waveform80/blinkenxmas/blinkenxmas/no-preview.png

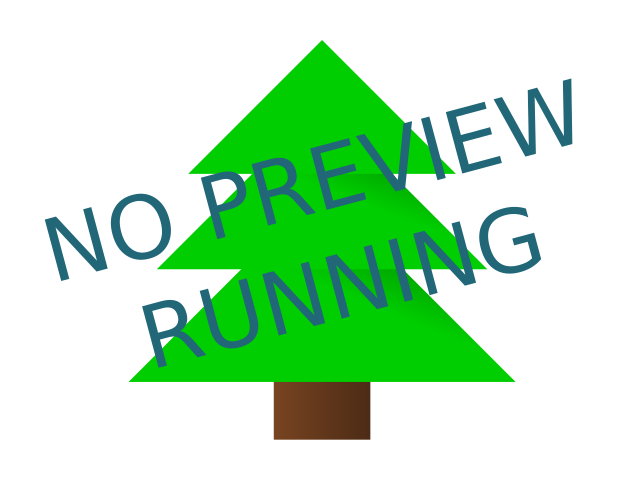
blinkenxmas/no-preview.png
